atwardzik/reflow_station_pcb/parts_external/1707027.stp

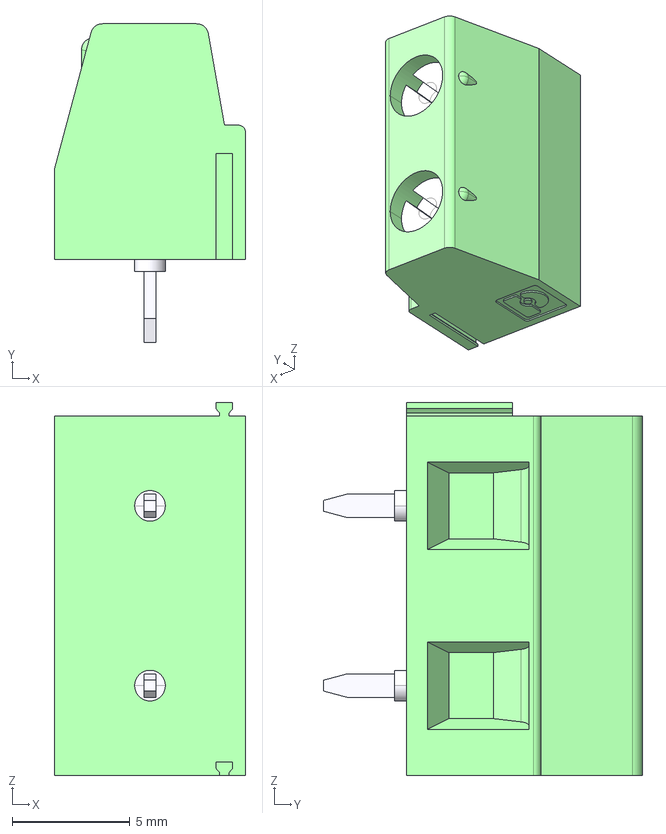
[picture p15: CAD file, 2026-09-16]
parts_external/1707027.stp
8.10 x 13.5 x 15.8 mm
