atwardzik/reflow_station_pcb/parts_external/1731734.stp

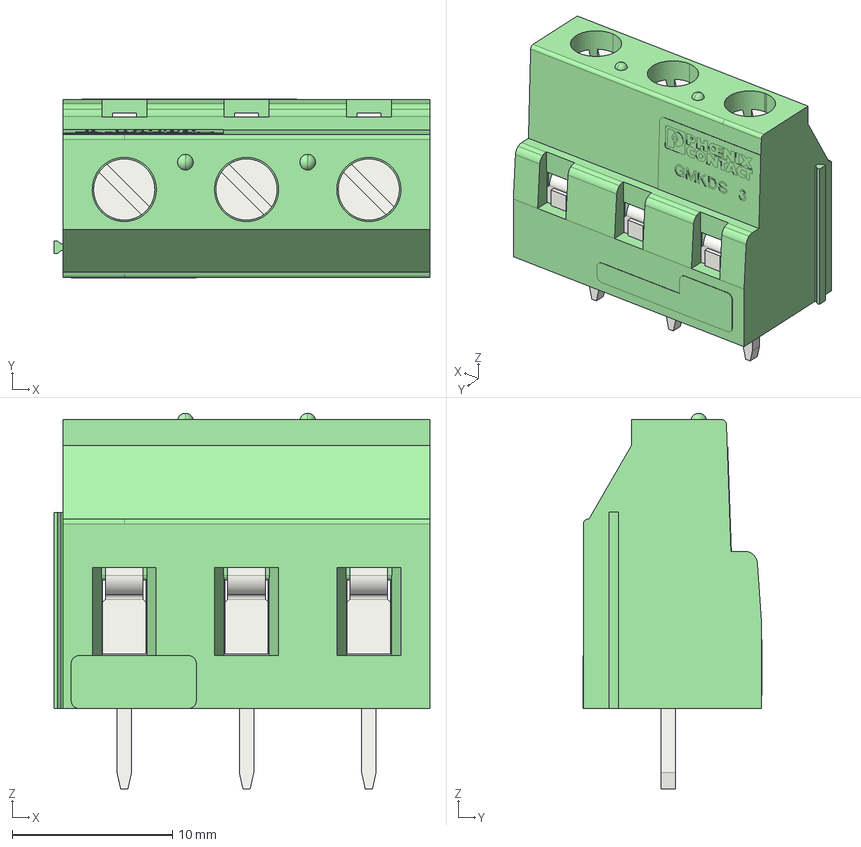
[picture p16: CAD file, 2026-09-13]
parts_external/1731734.stp
23.4 x 11.2 x 23.4 mm
